humberto9003/BarcoNRF24l01/PCB_BarcoV1.0/Draft1.asc

C1: polcap; 47µ; V=12.5 Irms=3.16228 Rser=0.025 Lser=0 mfg="KEMET" pn="A700D476M12RATE025" type="Al electrolytic"
C2: polcap; 22µ; V=10 Irms=354m Rser=0.2 Lser=0 mfg="KEMET" pn="T529P226M010AAE200" type="Tantalum"
C3: polcap; 100µ; V=12.5 Irms=4.33013 Rser=0.012 Lser=0 mfg="KEMET" pn="A700X107M12RATE012" type="Al electrolytic"
C4: polcap; 10µ; V=12.5 Irms=2.21565 Rser=0.055 Lser=0 mfg="KEMET" pn="A700V106M12RATE055" type="Al electrolytic"
D2: schottky; 1N5818
U1: LT1117-3.3
U2: LT1117-5
V1: battery; PULSE(6.4 8 0 0 0 0 2ms); Rser=100m
Named nets: 0
.tran 0 10ms 0 0.1ms
